logisim-evolution/GECKO5Education/kicad/GECKO5Education/3DModels/QFN_H-56Q-TRAY_FTD.step

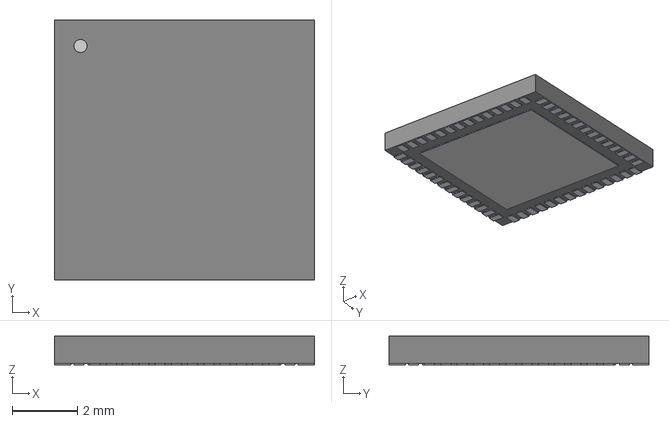
[picture p11: CAD file, 2023-06-18]
kicad/GECKO5Education/3DModels/QFN_H-56Q-TRAY_FTD.step
8.00 x 8.00 x 0.892 mm
