logisim-evolution/GECKO5Education/kicad/perifAddOn/3DModels/GTFP08431BEU.step

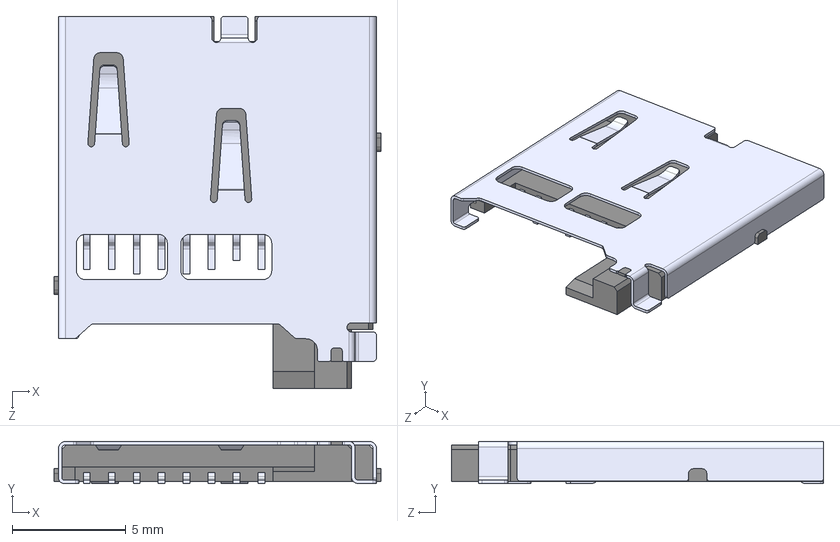
[picture p12: CAD file, 2024-01-29]
kicad/perifAddOn/3DModels/GTFP08431BEU.step
14.4 x 1.85 x 16.4 mm
