logisim-evolution/GECKO5Education/kicad/perifAddOn/3DModels/APHBM2012SURKCGKC.step

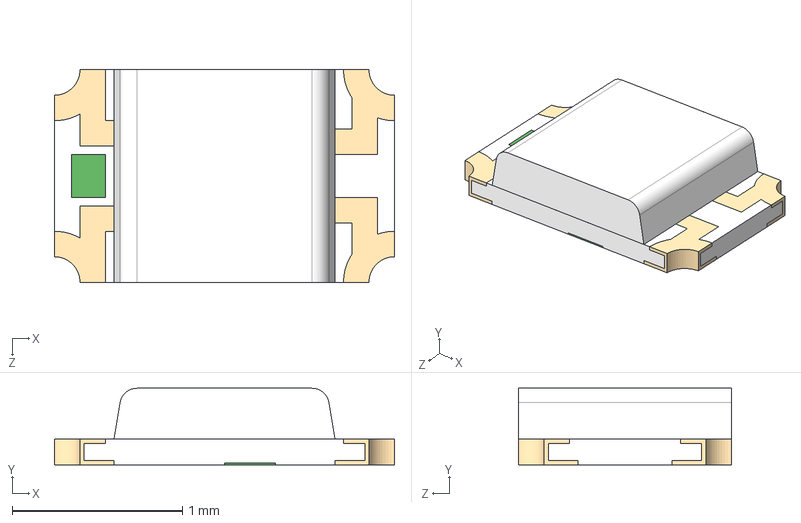
[picture p13: CAD file, 2024-01-29]
kicad/perifAddOn/3DModels/APHBM2012SURKCGKC.step
2.00 x 0.45 x 1.25 mm
