logisim-evolution/GECKO5Education/kicad/perifAddOn/3DModels/QFN36_6X6MC_MCH.step

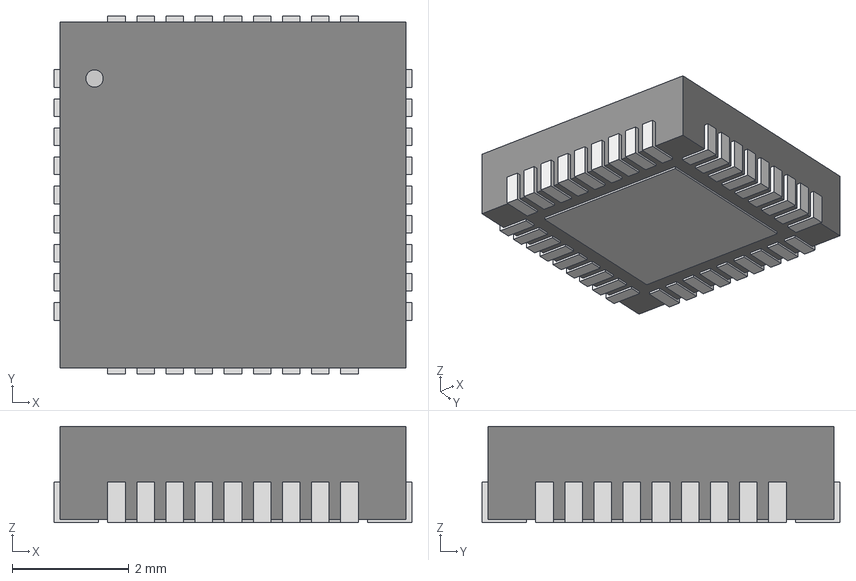
[picture p14: CAD file, 2024-01-29]
kicad/perifAddOn/3DModels/QFN36_6X6MC_MCH.step
6.15 x 6.15 x 1.65 mm
